trailblazer84562/IR_Driver/LTSpice/Beacon-Lantern Emitter/LanternEmitter.asc

D1: diode
D2: diode
D3: LED; TSAL7400
D4: LED; TSAL7400
D5: LED; TSAL7400
D6: LED; TSAL7400
M1: nmos; AONS32310
M2: nmos; Si7686DP
M3: pmos; SP8M5_P
R1: res; 1k
R2: res; 1k
R3: res; 3.4
R4: res; 320
R5: res; 80
R6: res; 1
U1: UniversalOpamp2; Avol=1Meg GBW=10Meg Slew=1Meg
V1: voltage; PULSE(9 6 0 {Duration} 0 100)
V2: voltage; PULSE(0.3 3.0 0 1n 1n {pulse} {period})
V3: voltage; 3.3V
V4: voltage; PULSE(3.0 0.3 0 10n 10n {Duration/2} {Duration*2/3})
Named nets: 0, Batt, Gate, Thresh
.tran 0 {Duration} 0 1n
.param  pulse 26.32u
.param period=26.32u*2
.model TSAL7400 D(Vfwd=1.6)
2S Lipo is 7.4 to 8.4
6 AA is 6.6 to 9.0V
6 NiMh is 6V to 7.2V
.param Duration=3m
