trailblazer84562/IR_Driver/LTSpice/Main and Secondary Emitter/Emitter.asc

C1: cap; 470µ
C2: cap; 470µ
C3: cap; 470µ
C4: cap; 470µ
D1: LED; TSAL6100
D2: LED; TSAL6100
D3: LED; TSAL6100
D4: LED; TSAL6100
D5: LED; TSAL6100
D6: LED; TSAL6100
D7: LED; TSAL6100
D8: LED; TSAL6100
Q1: pnp; BC807-40
Q2: npn; BCX54
Q3: npn; BCX54
Q4: npn; BCX54
Q5: npn; BCX54
R1: res; 10k
R2: res; 300
R3: res; 10k
R4: res; 4.7
R5: res; 1k
R6: res; 1
R7: res; 4.7
R8: res; 1k
R9: res; 1
R10: res; 4.7
R11: res; 1k
R12: res; 1
R13: res; 4.7
R14: res; 1k
R15: res; 1
V1: voltage; PULSE(3.3 0 0 5n 5n 0.5m 0.6m)
V2: voltage; PULSE(0 3.3 0 5n 5n 13.15u 26.3u)
V3: voltage; PWL(0 5.0 0.1 5.0)
Named nets: 0
.tran 0 0.01 0 100n
.model TSAL6100 D(Vfwd=1.5)
.model BCX54 npn is=3.06f bf=1.29e+02 nf=8.55e-01 vaf=7.24e+02 ikf=9.06e-01 ise=1.62e-16 ne=1 br=2.92 nr=9.10e-01 var=5.46e+01 ikr=1 isc=4.08e-14 nc=1 rb=1.65e+01 irb=2.38e-02 rbm=1.73e-02 re=1.26e-02 rc=3.11e-01 cje=1.17e-10 vje=3.00e-01 mje=4.22e-01 tf=1.42n xtf=7.75e-01 vtf=9.99e+05 itf=5.64e-01 cjc=4.85e-11 vjc=3.00e-01 mjc=5.09e-01 tr=1u xtb=0 eg=1.11 xti=3 fc=0.5 Vceo=45 Icrating=1 mfg=Philips
.MODEL Qmje3055t npn
+IS=1.92238e-13 BF=327.43 NF=0.85 VAF=36.105
+IKF=0.620037 ISE=1.4602e-10 NE=1.50926 BR=0.654697
+NR=0.935367 VAR=361.05 IKR=6.20037 ISC=6.85154e-12
+NC=2.96871 RB=16.05 IRB=0.1 RBM=0.161446
+RE=0.000602331 RC=0.0632768 XTB=0.943656 XTI=1.12302
+EG=1.05 CJE=9.23675e-08 VJE=0.506151 MJE=0.607139
+TF=1e-08 XTF=1.35736 VTF=0.997047 ITF=0.999796
+CJC=5e-10 VJC=0.400198 MJC=0.410184 XCJC=0.803125
+FC=0.658133 CJS=0 VJS=0.75 MJS=0.5
+TR=1e-07 PTF=0 KF=0 AF=1
